herve-tourrel/balance_connecte1/Images/1_tare.png

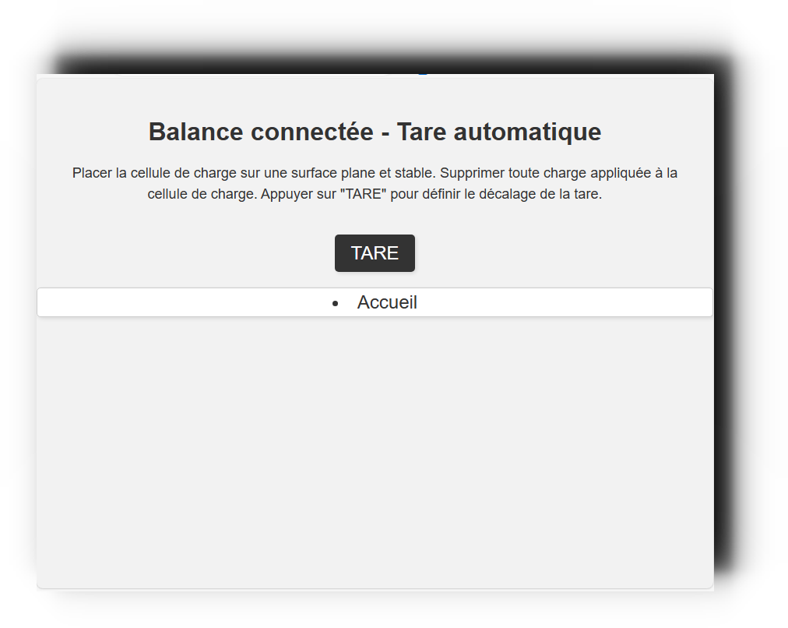
Images/1_tare.png
