herve-tourrel/balance_connecte1/Images/3_nom_ruche.png

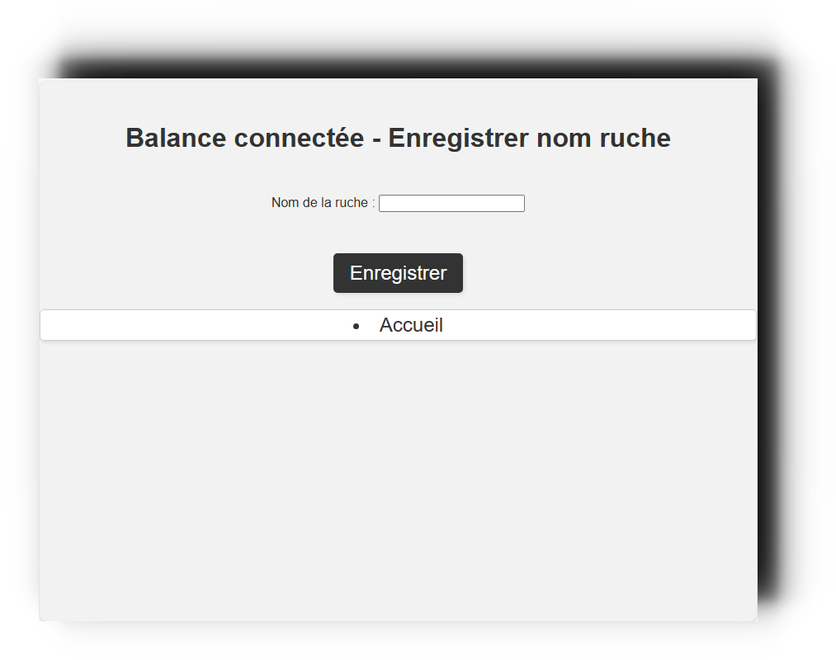
Images/3_nom_ruche.png
