herve-tourrel/balance_connecte1/Images/3_nom_ruche_rempli.png

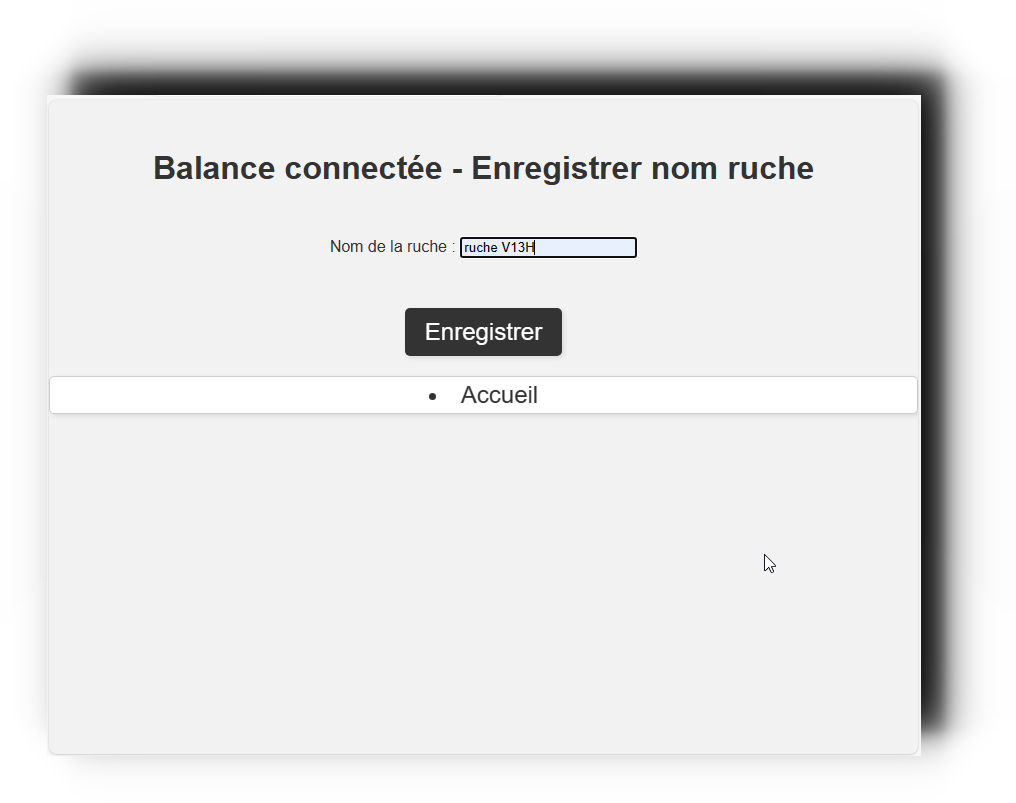
Images/3_nom_ruche_rempli.png
