herve-tourrel/balance_connecte1/Images/4_config_sms.png

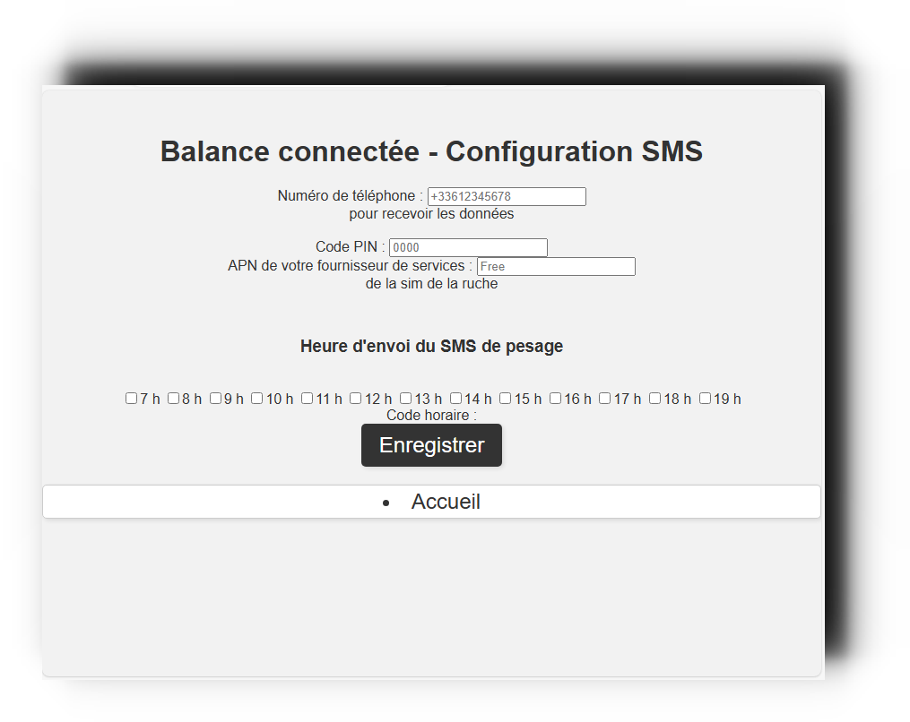
Images/4_config_sms.png
