herve-tourrel/balance_connecte1/Images/Jauge 200Kg.drawio.png

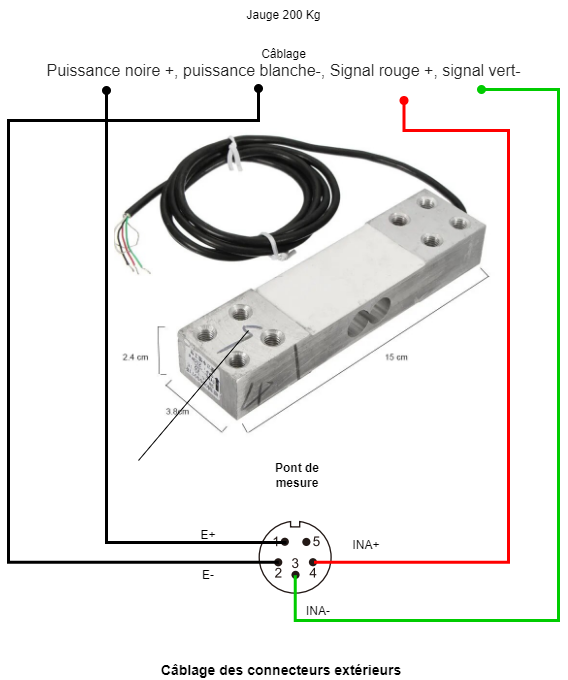
Images/Jauge 200Kg.drawio.png
