herve-tourrel/balance_connecte1/Images/origine_web/0_accueil.png

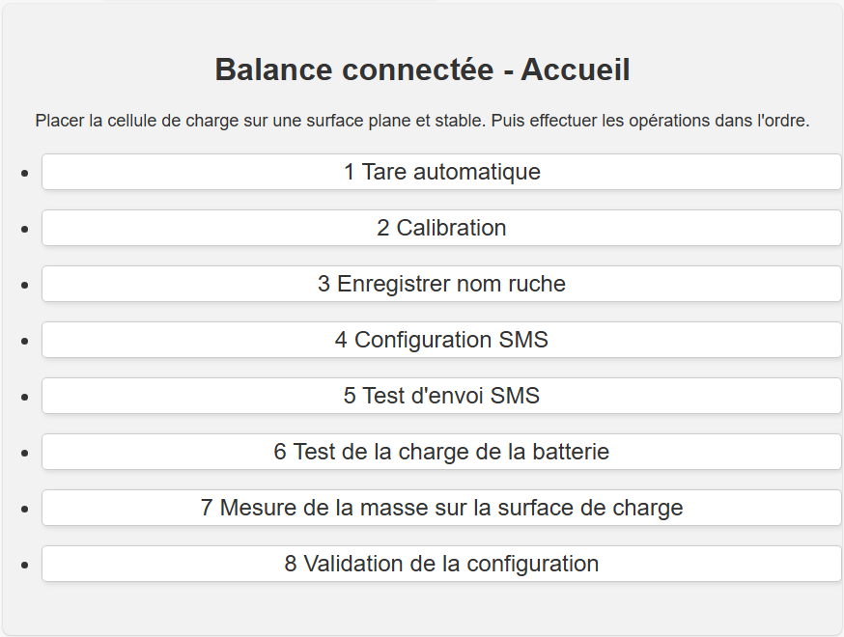
Images/origine_web/0_accueil.png
