herve-tourrel/balance_connecte1/Images/origine_web/1_tare.png

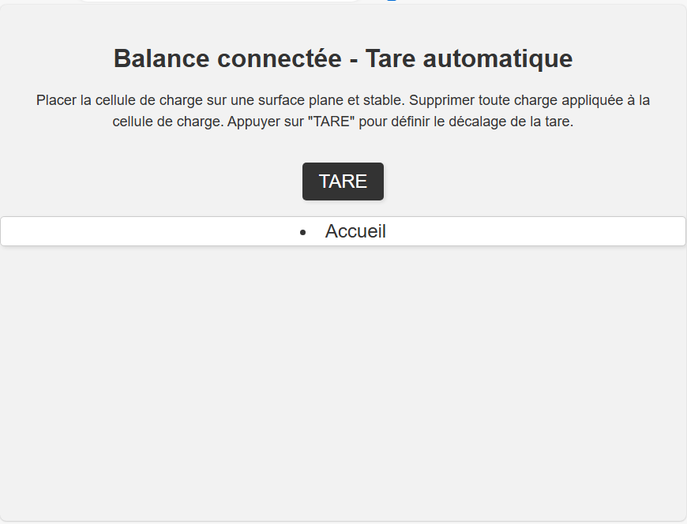
Images/origine_web/1_tare.png
