herve-tourrel/balance_connecte1/Images/origine_web/3_nom_ruche.png

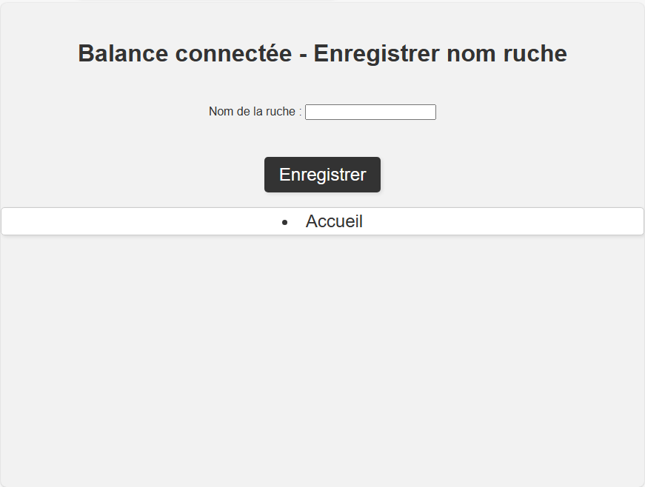
Images/origine_web/3_nom_ruche.png
