herve-tourrel/balance_connecte1/Images/origine_web/3_nom_ruche_rempli.png

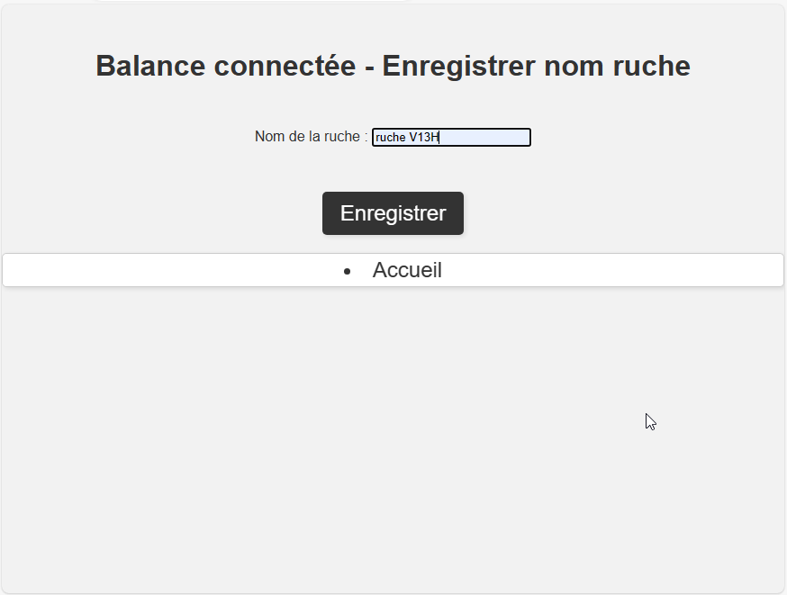
Images/origine_web/3_nom_ruche_rempli.png
