herve-tourrel/balance_connecte1/Images/origine_web/4_config_sms.png

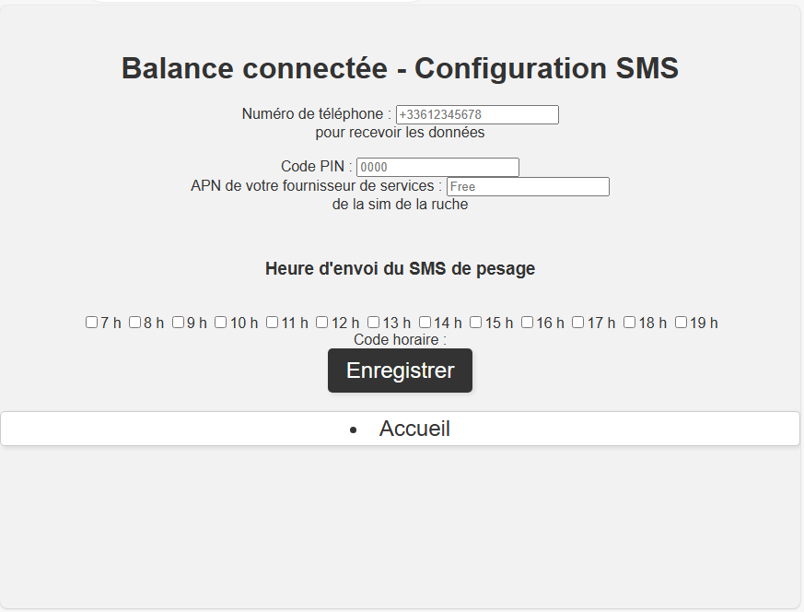
Images/origine_web/4_config_sms.png
