herve-tourrel/balance_connecte1/Images/origine_web/4_config_sms_rempli.png

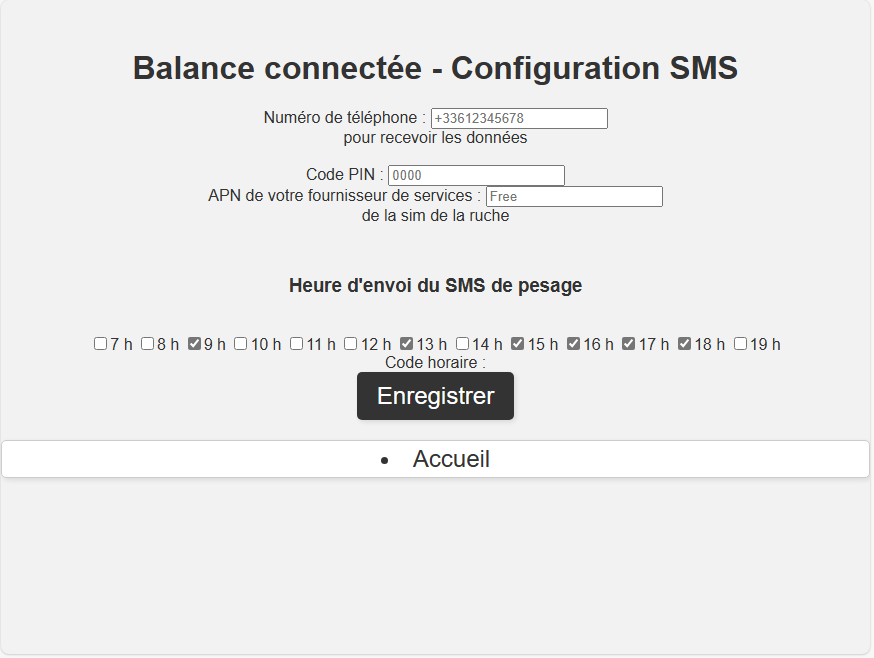
Images/origine_web/4_config_sms_rempli.png
