herve-tourrel/balance_connecte1/Images/origine_web/7_mesure_masse.png

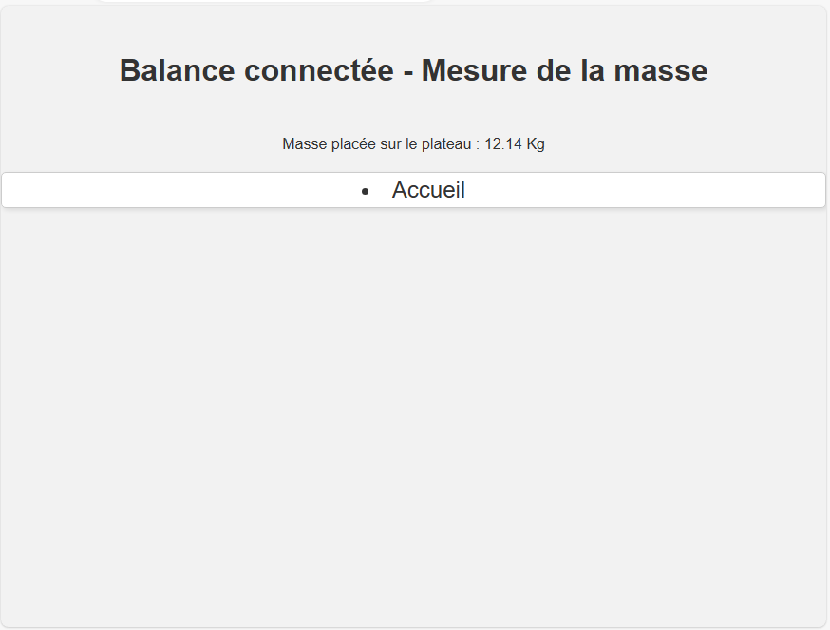
Images/origine_web/7_mesure_masse.png
