herve-tourrel/balance_connecte1/Images/2_calibration_reponse.png

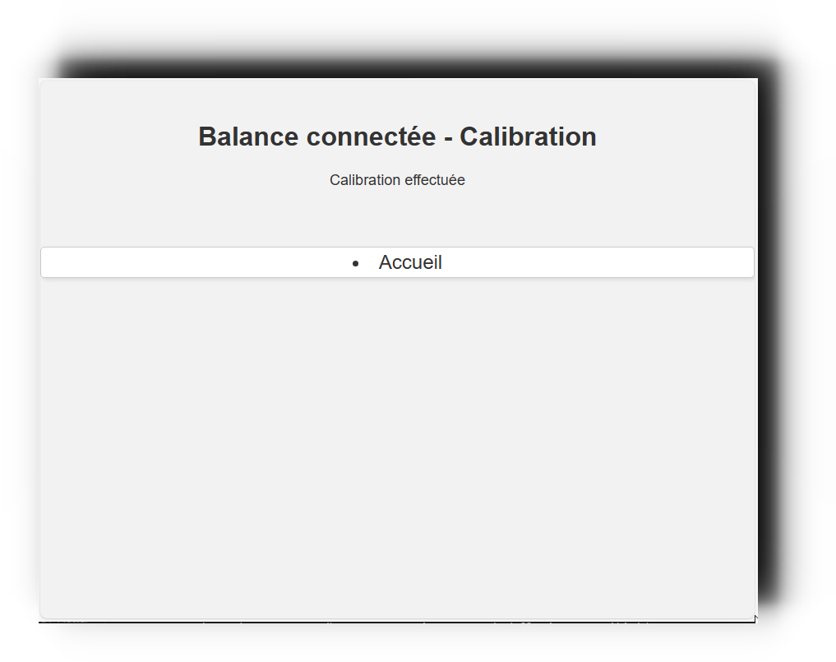
Images/2_calibration_reponse.png
