herve-tourrel/balance_connecte1/Images/origine_web/5_test_sms_reponse.png

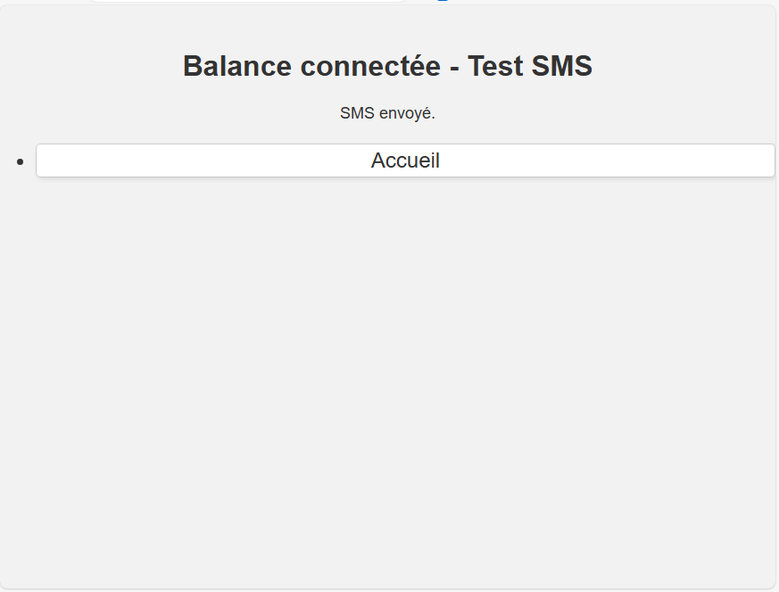
Images/origine_web/5_test_sms_reponse.png
